rctngl/dallas/hardware/dallas-controller/dallas-controller.kicad_sch

## KiCad design hardware/dallas-controller/dallas-controller.kicad_sch (2025-04-22)

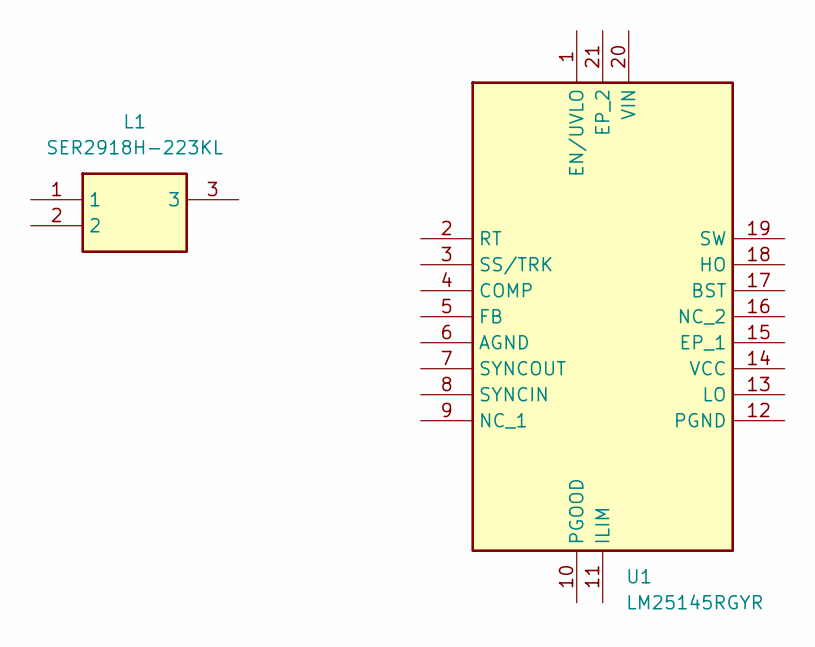
[picture p3: schematic dallas-controller.kicad_sch]

Parts:
L1: SER2918H-223KL; SER2918H223KL; Mouser Part Number 994-SER2918H-223KL
U1: LM25145RGYR; RGY0020B; Mouser Part Number 595-LM25145RGYR
